isocserbia/Klimerko-Pro/extras/photos/8.jpeg

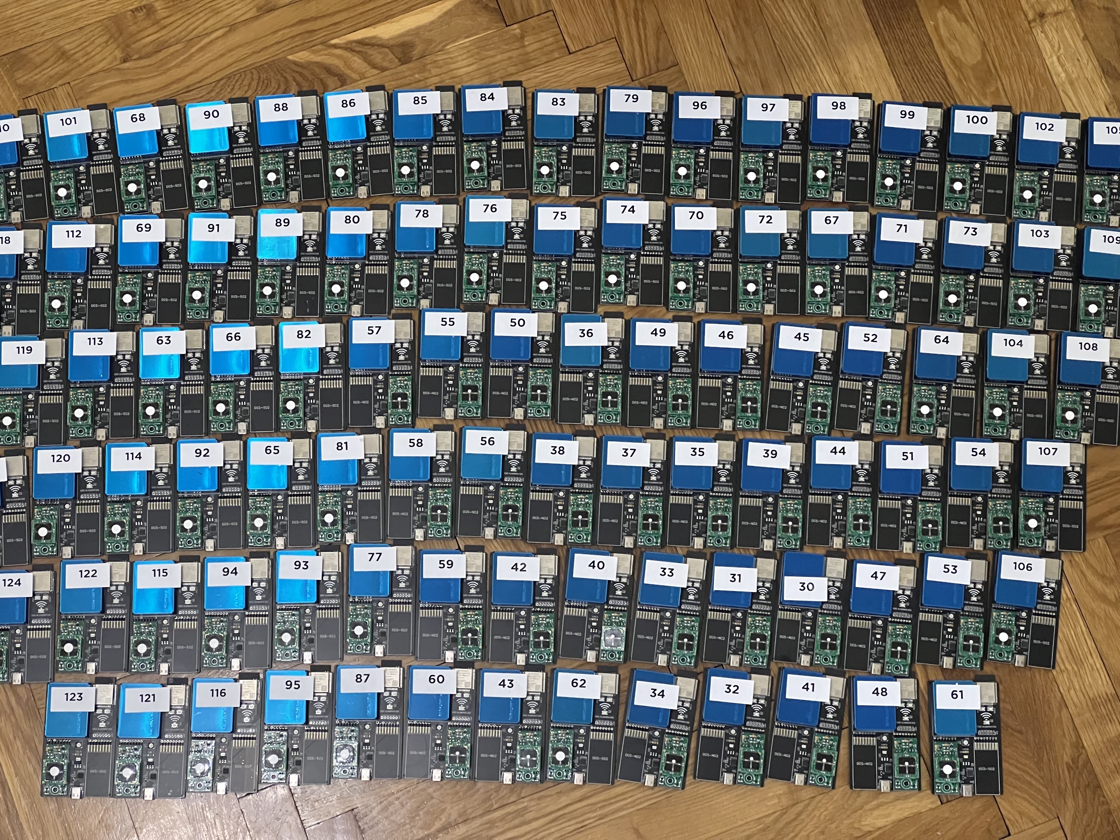
extras/photos/8.jpeg
